yik3z/Watchy-CAD/Pictures/SlimV4/20210927_175707.jpg

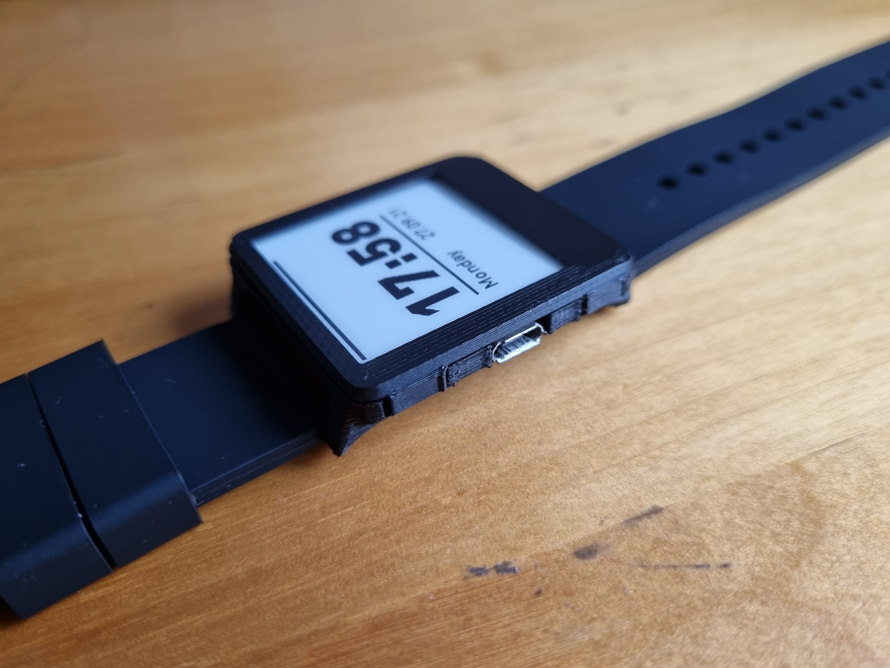
Pictures/SlimV4/20210927_175707.jpg
