yik3z/Watchy-CAD/Touchscreen Mod/Touchscreen/Test Code/Touchscreen test/packages_dir/framework-arduinoespressif32/tools/partitions/ffat.csv

# Name | Type | SubType | Offset | Size | Flags
nvs | data | nvs | 0x9000 | 0x5000
otadata | data | ota | 0xe000 | 0x2000
app0 | app | ota_0 | 0x10000 | 0x200000
app1 | app | ota_1 | 0x210000 | 0x200000
ffat | data | fat | 0x410000 | 0xBF0000
# to create/use ffat | see https://github.com/marcmerlin/esp32_fatfsimage
