yik3z/Watchy-CAD/Touchscreen Mod/E paper display/154M09 Sample Code (STM32)/Ap_29demo.h

/////////////�ֲ�ˢ��ͼƬ//////////////////////
//64*32(y=64-1,x=32-1)
const unsigned char gImage_num1[256] = { /* 0X81,0X01,0X20,0X00,0X20,0X00, */
//1
0XFF,0XFF,0XFF,0XFF,0XFF,0XFF,0XFF,0XFF,0XFF,0XFF,0XFF,0XFF,0XFF,0XFF,0XFF,0XFF,
0XFF,0XFF,0XFF,0XFF,0XFF,0XFF,0XFF,0XFF,0XFF,0XFF,0XFF,0XFF,0XFF,0XFF,0XFF,0XFF,
0XFF,0XFF,0XFF,0XFF,0XFF,0XFF,0XFF,0XFF,0XFF,0XFF,0XFF,0XF7,0XFF,0XFF,0XFF,0XF7,
0XFF,0XFF,0XFF,0XF7,0XFF,0XFF,0XFF,0XE7,0XFF,0X00,0X00,0X07,0XFF,0X00,0X00,0X07,
0XFF,0X80,0X00,0X07,0XFF,0XDF,0XFF,0XE7,0XFF,0XDF,0XFF,0XF7,0XFF,0XDF,0XFF,0XF7,
0XFF,0XDF,0XFF,0XF7,0XFF,0XFF,0XFF,0XFF,0XFF,0XFF,0XFF,0XFF,0XFF,0XFF,0XFF,0XFF,
0XFF,0XFF,0XFF,0XFF,0XFF,0XFF,0XFF,0XFF,0XFF,0XFF,0XFF,0XFF,0XFF,0XFF,0XFF,0XFF,
0XFF,0XFF,0XFF,0XFF,0XFF,0XFF,0XFF,0XFF,0XFF,0XFF,0XFF,0XFF,0XFF,0XFF,0XFF,0XFF,
//0
0XFF,0XFF,0XFF,0XFF,0XFF,0XFF,0XFF,0XFF,0XFF,0XFF,0XFF,0XFF,0XFF,0XFF,0XFF,0XFF,
0XFF,0XFF,0XFF,0XFF,0XFF,0XFF,0XFF,0XFF,0XFF,0XFF,0XFF,0XFF,0XFF,0XFF,0XFF,0XFF,
0XFF,0XFC,0X01,0XFF,0XFF,0XE0,0X00,0X3F,0XFF,0XC0,0X00,0X1F,0XFF,0X87,0XFF,0X0F,
0XFF,0X1F,0XFF,0XC7,0XFF,0X3F,0XFF,0XE7,0XFF,0X7F,0XFF,0XF7,0XFF,0X7F,0XFF,0XF7,
0XFF,0X3F,0XFF,0XE7,0XFF,0X1F,0XFF,0XC7,0XFF,0X83,0XFE,0X0F,0XFF,0XC0,0X00,0X1F,
0XFF,0XE0,0X00,0X3F,0XFF,0XFC,0X01,0XFF,0XFF,0XFF,0XFF,0XFF,0XFF,0XFF,0XFF,0XFF,
0XFF,0XFF,0XFF,0XFF,0XFF,0XFF,0XFF,0XFF,0XFF,0XFF,0XFF,0XFF,0XFF,0XFF,0XFF,0XFF,
0XFF,0XFF,0XFF,0XFF,0XFF,0XFF,0XFF,0XFF,0XFF,0XFF,0XFF,0XFF,0XFF,0XFF,0XFF,0XFF,
};

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
0XFF,0XFF,0XFF,0XFF,0XFF,0XFF,0XFF,0XFF,0XFF,0XFF,0XFF,0XFF,0XFF,0XFF,0XFF,0XFF,
0XFF,0XFF,0XFF,0XFF,0XFF,0XFF,0XFF,0XFF,0XFF,0XFF,0XFF,0XFF,0XFF,0XFF,0XFF,0XFF,
0XFF,0XFF,0XFF,0XFF,0XFF,0XFF,0XFF,0XFF,0XFF,0XFF,0XFF,0XFF,0XFF,0XFF,0XFF,0XFF,
0XFF,0XFF,0XFF,0XFF,0XFF,0XFF,0XFF,0XFF,};
