yik3z/Watchy-CAD/Touchscreen Mod/E paper display/154M09 Sample Code (STM32)/Display_EPD_W21_spi.c

#include "Display_EPD_W21_spi.h"


void EPD_GPIO_Init(void)
{
	GPIO_InitTypeDef  GPIO_InitStructure;
 	
	RCC_APB2PeriphClockCmd(RCC_APB2Periph_GPIOD|RCC_APB2Periph_GPIOE, ENABLE);
	  				     	
	
	 //CS-->PD8   SCK-->PD9  SDO--->PD10 
	GPIO_InitStructure.GPIO_Pin = GPIO_Pin_8|GPIO_Pin_9|GPIO_Pin_10;		//Port configuration
	GPIO_InitStructure.GPIO_Mode = GPIO_Mode_Out_PP; 		 			
	GPIO_InitStructure.GPIO_Speed = GPIO_Speed_2MHz;		 		
	GPIO_Init(GPIOD, &GPIO_InitStructure);	  	
		
	 // D/C--->PE15	   RES-->PE14
	GPIO_InitStructure.GPIO_Pin = GPIO_Pin_14|GPIO_Pin_15;		//Port configuration
	GPIO_InitStructure.GPIO_Mode = GPIO_Mode_Out_PP; 		 			
	GPIO_InitStructure.GPIO_Speed = GPIO_Speed_2MHz;		 		
	GPIO_Init(GPIOE, &GPIO_InitStructure);	  				     		
	
	// BUSY--->PE13
	GPIO_InitStructure.GPIO_Pin  = GPIO_Pin_13;
	GPIO_InitStructure.GPIO_Mode = GPIO_Mode_IPU;	//Pull up input
	GPIO_InitStructure.GPIO_Speed = GPIO_Speed_2MHz;
 	GPIO_Init(GPIOE, &GPIO_InitStructure);				//Initialize GPIO
	
	 //LED 
	GPIO_InitStructure.GPIO_Pin = GPIO_Pin_12;		//Port configuration
	GPIO_InitStructure.GPIO_Mode = GPIO_Mode_Out_PP; 		 			
	GPIO_InitStructure.GPIO_Speed = GPIO_Speed_2MHz;		 		
	GPIO_Init(GPIOE, &GPIO_InitStructure);
}

void SPI_Delay(unsigned char xrate)
{
	while(xrate--);

}


void SPI_Write(unsigned char value)                                    
{                                                           
	unsigned char i;
	 SPI_Delay(1);
	for(i=0; i<8; i++)   
	{
		EPD_W21_CLK_0;
		SPI_Delay(1);
		if(value & 0x80)
			EPD_W21_MOSI_1;
		else
			EPD_W21_MOSI_0;		
		value = (value << 1);
		SPI_Delay(1);				
		EPD_W21_CLK_1;
		SPI_Delay(1);				
	}
}

void EPD_W21_WriteCMD(unsigned char command)
{
	SPI_Delay(1);
  EPD_W21_CS_0;                   
	EPD_W21_DC_0;		// command write
	SPI_Write(command);
	EPD_W21_CS_1;
}
void EPD_W21_WriteDATA(unsigned char data)
{
	SPI_Delay(1);
  EPD_W21_CS_0;                   
	EPD_W21_DC_1;		// data write
	SPI_Write(data);
	EPD_W21_CS_1;
}



/***********************************************************
						end file
***********************************************************/
