yik3z/Watchy-CAD/Pictures/20210927_175304.jpg

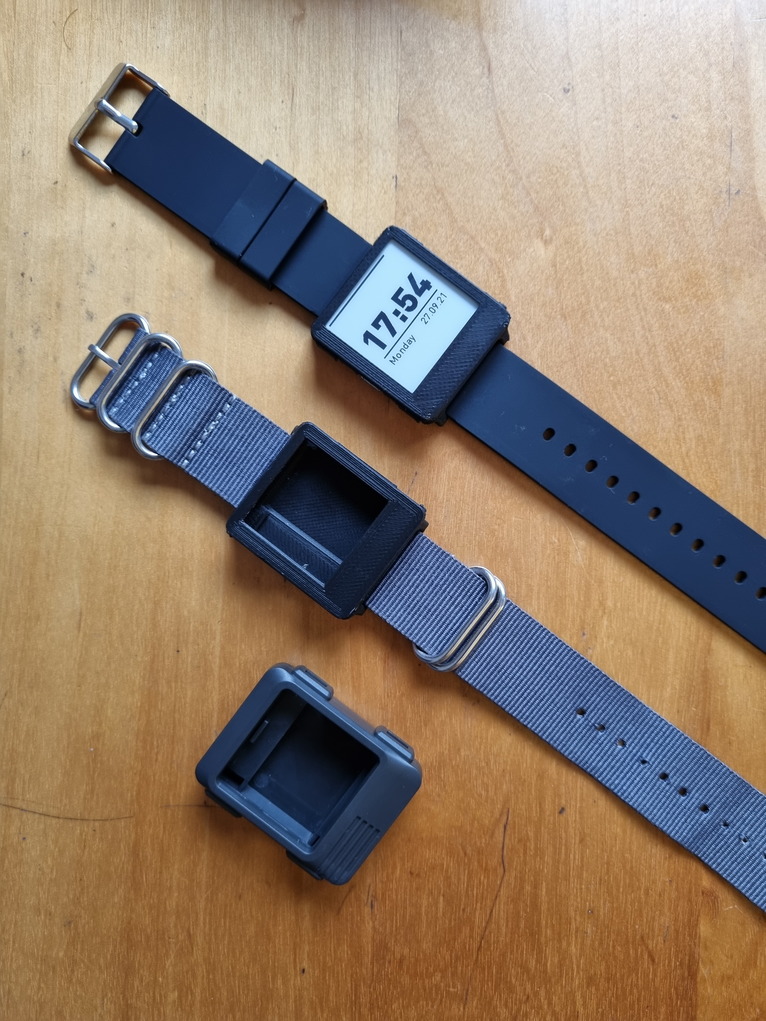
Pictures/20210927_175304.jpg
