yik3z/Watchy-CAD/Pictures/SlimV4/20220923_174231.jpg

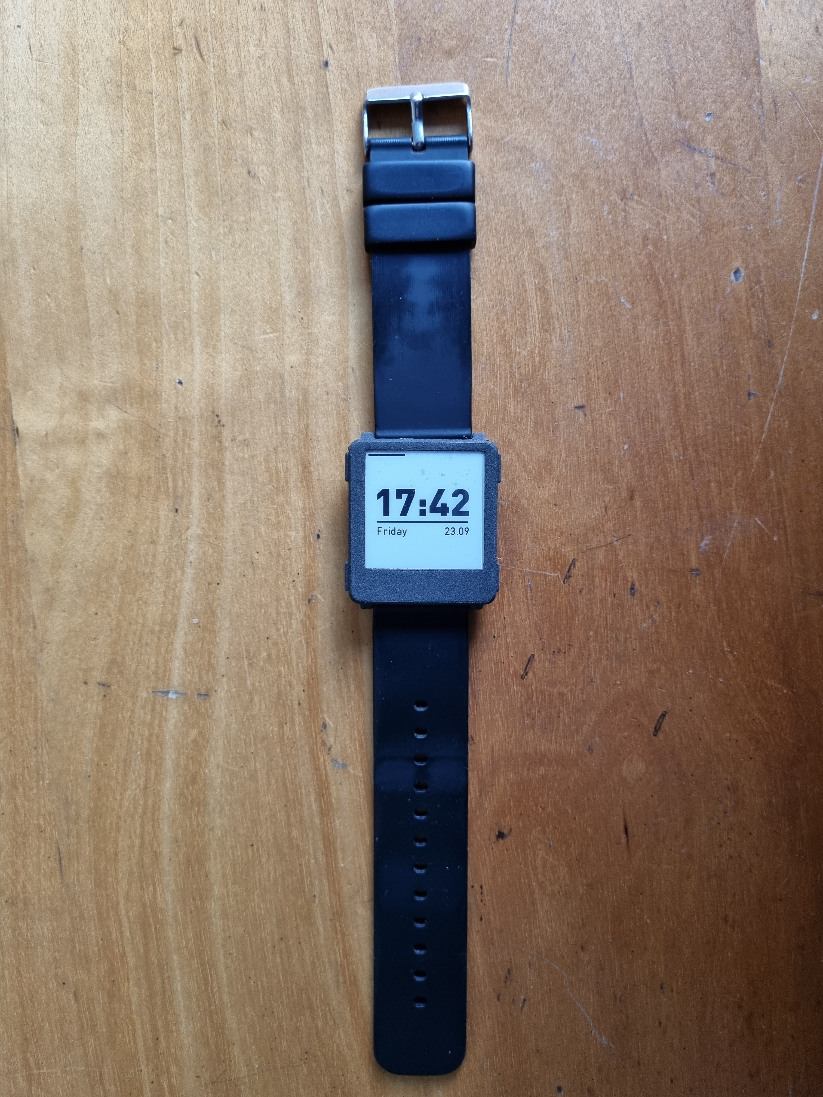
Pictures/SlimV4/20220923_174231.jpg
