yik3z/Watchy-CAD/Pictures/SlimV4/20220923_174238.jpg

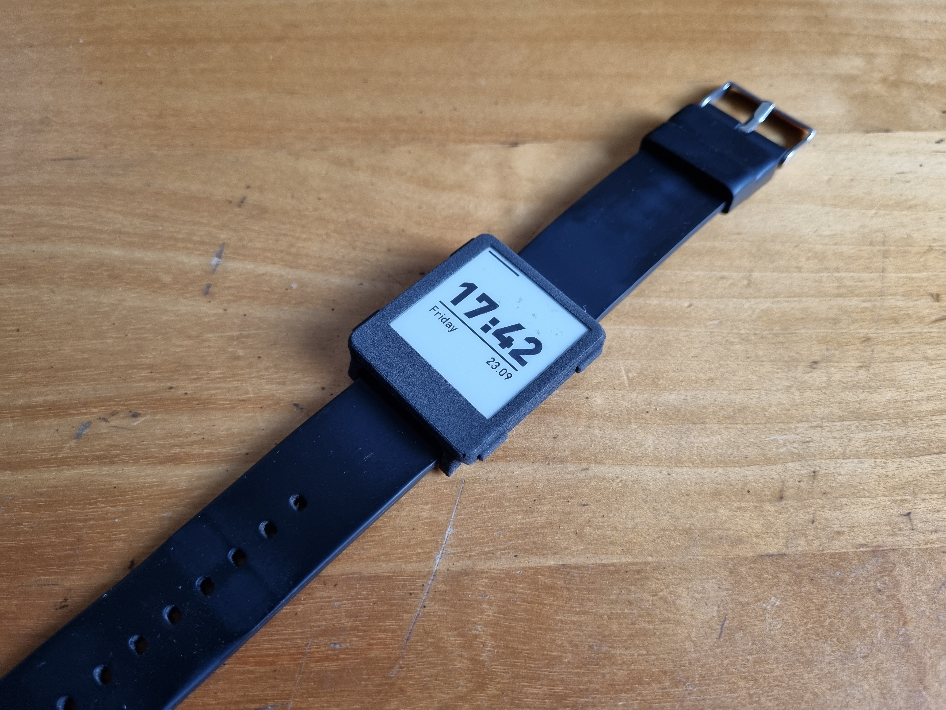
Pictures/SlimV4/20220923_174238.jpg
